mcflan/z80_monitor/host/monitor.py

#!/usr/bin/env python3
#

# Host code for Z80 monitor
# J.Macfarlane 2020.

import serial, sys, argparse

MSG_WR              = 0x01
MSG_RD              = 0x02
MSG_CLEAR           = 0x03
MSG_BUS_REQ         = 0x04
MSG_BUS_REL         = 0x05
MSG_RESET           = 0x06
MSG_NMI             = 0x07
MSG_INT             = 0x08

ADDRSPACE_MEM = 0
ADDRSPACE_IO = 1

# Given a byte array, turn all bytes into printable ASCII characters by
# converting non-printable ones to spaces. There is no trivial way to do this
# in modern python due to the empracing of unicode, etc. So we'll take a
# shortcut :P
def printable(b):
    pb = bytes([ x if x >= 0x20 and x < 0x7f else 0x20 for x in b])
    return pb.decode('utf-8')

# Pretty-print 16 bytes of data, showing address, hex and ASCII outputs
def pretty(addr: int, data: bytearray):
    count = len(data)
    print("{:04X} ".format(addr), end='')
    for b in data:
        print(" {:02X}".format(b), end='')
    print("   "*(16-count), end='')
    print("  ", printable(data))


class Message(object):
    def __init__(self, mtype, data):
        self.type = mtype
        self.data = data

    @classmethod
    def from_msg(cls, line):
        # line is a bytearray received by the serial module.
        # We need to convert it to a string first and remove
        # the linefeed.
        try:
            msg = line.decode('utf-8').rstrip()
        except UnicodeDecodeError:
            print("Decode error for msg '{}'".format(line))
            return None
        if msg[0] == '#':
            print(msg)
            return None
        if msg[0] != ':':
            print("Message didn't start with ':' - '{}'".format(msg))
            return None
        # Now attempt to decode as ASCII hex
        try:
            raw = bytes.fromhex(msg[1:])
        except:
            print("Couldn't decode message as hex - '{}'".format(msg))
            return None

        chksum = sum(raw) % 256
        if chksum != 0:
            print("checksum error on message - '{}'".format(msg))
            return None
        mtype = raw[0]
        mdata = raw[1:-1]
        return cls(mtype, mdata)


def get_msg(port):
    resp = ser.readline()
    if len(resp) == 0:
        print("Timeout\n")
        return None
    return Message.from_msg(resp)

def get_resp(port, mtype):
    resp = get_msg(port)
    if resp:
        if resp.type == 2:
            addr = int.from_bytes(resp.data[0:2], byteorder='little')
            pretty(addr, resp.data[2:])
        else: 
            print("Got response type {}".format(resp.type))

def send_msg(port, mtype, msg: bytearray = None):
    # Prepend type byte
    type_stub = mtype.to_bytes(length=1, byteorder='little')
    if msg is None:
        msg = type_stub
    else:
        msg = type_stub + msg
    chksum = (256 - sum(msg) % 256) % 256
    msg += chksum.to_bytes(length=1, byteorder='little')
    enc = b':' + msg.hex().encode('utf-8') + b'\n'
    port.write(enc)
    get_resp(port, mtype)

# Parse a line from an Intel hex file
def unhex(line):
    chksum = sum(bytes.fromhex(line[1:-1])) % 256
    if chksum != 0:
        print("checksum error")
        return None
    type = int(line[7:9],16)
    length = int(line[1:3],16)
    addr = int(line[3:7],16)
    #print("{} 0x{:04X} {:2d}".format(type, addr, length))
    if type == 0:
        data = bytes.fromhex(line[9:-3])
        msg = ADDRSPACE_MEM.to_bytes(length=1, byteorder='little')
        msg += addr.to_bytes(length=2, byteorder='little')
        msg += data
        return msg
    return None

def auto_int(x):
    return int(x, 0)

def send_read_msg(port, memtype, addr, size):
    msg = memtype.to_bytes(length=1, byteorder='little')
    if addr < 0 or addr > 0xffff:
        raise OverflowError('Address 0x{:05X} is out of range'.format(addr))
    msg += addr.to_bytes(length=2, byteorder='little')
    msg += size.to_bytes(length=1, byteorder='little')
    send_msg(ser, MSG_RD, msg)

def send_clear_msg(port, memtype, addr, size, value):
    msg = memtype.to_bytes(length=1, byteorder='little')
    if addr < 0 or addr > 0xffff:
        raise OverflowError('Address 0x{:05X} is out of range'.format(addr))
    if size < 0 or size > 0xffff:
        raise OverflowError('Count 0x{:05X} is out of range'.format(count))
    msg += addr.to_bytes(length=2, byteorder='little')
    msg += size.to_bytes(length=2, byteorder='little')
    msg += value.to_bytes(length=1, byteorder='little')
    send_msg(ser, MSG_CLEAR, msg)


parser = argparse.ArgumentParser(description="Z80 Monitor")
parser.add_argument('-b', '--baud', metavar='baud', type=int,
                    default=115200, help='Baud Rate')
parser.add_argument('-r', '--read', metavar=('addr','count'), type=auto_int, nargs=2,
                    default=None, help='Read from addr')
parser.add_argument('-c', '--clear', metavar=('addr', 'count', 'value'), type=auto_int, nargs=3,
                    default=None, help='Clear all memory in range to constant value')
parser.add_argument('-R', '--reset', action='store_true', help='Reset target before releasing bus.')
parser.add_argument('-N', '--nmi', action='store_true', help='Cycle NMI line')
parser.add_argument('-I', '--int', action='store_true', help='Cycle INT line')
parser.add_argument('-p', '--port', type=str, help='Serial port', required=True)
parser.add_argument('files', type=str, nargs='*',
                    help='Intel Hex File')

args = parser.parse_args()

# Open port initially with a small timeout to clear any junk
# data. The API does not seem to provide a nice way to do
# this. The seemingly promising 'reset_input_buffer()'
# doesn't.
ser = serial.Serial(args.port, args.baud, timeout=0.05)
while ser.read(): pass
ser.close()

ser = serial.Serial(args.port, args.baud, timeout=1)

if args.nmi:
    send_msg(ser, MSG_NMI);
    sys.exit(0)

if args.int:
    send_msg(ser, MSG_INT);
    sys.exit(0)

send_msg(ser, MSG_BUS_REQ)

if args.clear is not None:
    start_addr = args.clear[0]
    count = args.clear[1]
    value = args.clear[2]
    send_clear_msg(ser, ADDRSPACE_MEM, start_addr, count, value)

if args.read is not None:
    start_addr = args.read[0]
    count = args.read[1]
    for i in range(0,count,16):
        send_read_msg(ser, ADDRSPACE_MEM, start_addr+i, min(count-i, 16))

for name in args.files:
    with open(name) as f:
        for line in f:
            msg = unhex(line)
            if msg is not None:
                send_msg(ser, MSG_WR, msg)

if args.reset:
    send_msg(ser, MSG_RESET) # Also releases bus
else:
    send_msg(ser, MSG_BUS_REL)

ser.close()
