mcflan/z80_monitor/src/monitor.h

#ifndef MONITOR_H
#define MONITOR_H

#define MSG_WR              (0x01)
#define MSG_RD              (0x02)
#define MSG_CLEAR           (0x03)
#define MSG_BUS_REQ         (0x04)
#define MSG_BUS_REL         (0x05)
#define MSG_RESET           (0x06)
#define MSG_NMI             (0x07)
#define MSG_INT             (0x08)

#define ADDRSPACE_MEM       (0)
#define ADDRSPACE_IO        (1)

#endif // MONITOR_H
